koupypavel/xkboard/xkboard_mcu/firmware/examples/10_xkboard_mcu_4327/src/board_sysinit.c

/*
 * board_sysinit.c
 *
 *  Created on: 28. 6. 2021
 *      Author: xkoupy00
 */

#include "board.h"

/* The System initialization code is called prior to the application and
   initializes the board for run-time operation. Board initialization
   includes clock setup and default pin muxing configuration. */

/*****************************************************************************
 * Private types/enumerations/variables
 ****************************************************************************/

/* Structure for initial base clock states */
struct CLK_BASE_STATES {
	CHIP_CGU_BASE_CLK_T clk;	/* Base clock */
	CHIP_CGU_CLKIN_T clkin;	/* Base clock source, see UM for allowable souorces per base clock */
	bool autoblock_enab;/* Set to true to enable autoblocking on frequency change */
	bool powerdn;		/* Set to true if the base clock is initially powered down */
};

//uncomment and commnet what ever you please, is commented out for safety reason
STATIC const PINMUX_GRP_T pinmuxing[] = {

	/* Board LEDs */
	/*D5*/{0x6, 7, (SCU_MODE_INBUFF_EN | SCU_MODE_PULLUP | SCU_MODE_FUNC4)},
	/*D6*/{0x6, 9, (SCU_MODE_INBUFF_EN | SCU_MODE_PULLUP | SCU_MODE_FUNC0)},
	/*D7*/{0x6, 11, (SCU_MODE_INBUFF_EN | SCU_MODE_PULLUP | SCU_MODE_FUNC0)},

	/* Buttons */
	/*SW3*/{0x6, 3, (SCU_MODE_PULLUP | SCU_MODE_INBUFF_EN | SCU_MODE_ZIF_DIS | SCU_MODE_FUNC0)},
	/*SW4*/{0x6, 6, (SCU_MODE_PULLUP | SCU_MODE_INBUFF_EN | SCU_MODE_ZIF_DIS | SCU_MODE_FUNC0)},

	/* ARDUINO header */
//	/*0*/{0x1, 13, (SCU_MODE_INBUFF_EN | SCU_MODE_PULLUP | SCU_MODE_FUNC4)},
//	/*1*/{0x1, 14, (SCU_MODE_INBUFF_EN | SCU_MODE_PULLUP | SCU_MODE_FUNC0)},
//	/*2*/{0x1, 16, (SCU_MODE_INBUFF_EN | SCU_MODE_PULLUP | SCU_MODE_FUNC0)},
//	/*3*/{0x5, 0, (SCU_MODE_INBUFF_EN | SCU_MODE_PULLUP | SCU_MODE_FUNC4)},
	/*4*/{0x1, 17, (SCU_MODE_INBUFF_EN | SCU_MODE_PULLUP | SCU_MODE_FUNC0)},
	/*5*/{0x5, 4, (SCU_MODE_INBUFF_EN | SCU_MODE_PULLUP | SCU_MODE_FUNC0)},
	/*6*/{0x5, 5, (SCU_MODE_INBUFF_EN | SCU_MODE_PULLUP | SCU_MODE_FUNC0)},
	/*7*/{0x1, 15, (SCU_MODE_INBUFF_EN | SCU_MODE_PULLUP | SCU_MODE_FUNC0)},
	/*8*/{0x1, 18, (SCU_MODE_INBUFF_EN | SCU_MODE_PULLUP | SCU_MODE_FUNC0)},
//	/*9*/{0x5, 6, (SCU_MODE_INBUFF_EN | SCU_MODE_PULLUP | SCU_MODE_FUNC0)},
//	/*10*/{0x3, 2, (SCU_MODE_INBUFF_EN | SCU_MODE_PULLUP | SCU_MODE_FUNC0)},
//	/*11*/{0x3, 7, (SCU_MODE_INBUFF_EN | SCU_MODE_PULLUP | SCU_MODE_FUNC0)},
//	/*12*/{0x3, 6, (SCU_MODE_INBUFF_EN | SCU_MODE_PULLUP | SCU_MODE_FUNC0)},
//	/*13*/{0x3, 3, (SCU_MODE_INBUFF_EN | SCU_MODE_PULLUP | SCU_MODE_FUNC0)},

	/* LPC MCU I/O header*/
//	/*1*/{0x9, 6, (SCU_MODE_INBUFF_EN | SCU_MODE_PULLUP | SCU_MODE_FUNC0)},
//	/*2*/{0x9, 5, (SCU_MODE_INBUFF_EN | SCU_MODE_PULLUP | SCU_MODE_FUNC0)},
//	/*3*/{0x2, 0, (SCU_MODE_INBUFF_EN | SCU_MODE_PULLUP | SCU_MODE_FUNC4)},
//	/*4*/{0x2, 1, (SCU_MODE_INBUFF_EN | SCU_MODE_PULLUP | SCU_MODE_FUNC0)},
//	/*5*/{0x2, 2, (SCU_MODE_INBUFF_EN | SCU_MODE_PULLUP | SCU_MODE_FUNC0)},
//	/*6*/{0x2, 3, (SCU_MODE_INBUFF_EN | SCU_MODE_PULLUP | SCU_MODE_FUNC4)},
//	/*7*/{0x2, 4, (SCU_MODE_INBUFF_EN | SCU_MODE_PULLUP | SCU_MODE_FUNC0)},
//	/*8*/{0x2, 5, (SCU_MODE_INBUFF_EN | SCU_MODE_PULLUP | SCU_MODE_FUNC0)},
//	/*9*/{0x2, 6, (SCU_MODE_INBUFF_EN | SCU_MODE_PULLUP | SCU_MODE_FUNC0)},
//	/*10*/{0x1, 0, (SCU_MODE_INBUFF_EN | SCU_MODE_PULLUP | SCU_MODE_FUNC0)},
//	/*11*/{0x1, 3, (SCU_MODE_INBUFF_EN | SCU_MODE_PULLUP | SCU_MODE_FUNC0)},
//	/*12*/{0x1, 4, (SCU_MODE_INBUFF_EN | SCU_MODE_PULLUP | SCU_MODE_FUNC0)},
//	/*13*/{0x1, 5, (SCU_MODE_INBUFF_EN | SCU_MODE_PULLUP | SCU_MODE_FUNC0)},
//	/*14*/{0x1, 6, (SCU_MODE_INBUFF_EN | SCU_MODE_PULLUP | SCU_MODE_FUNC0)},
//	/*15*/{0x1, 7, (SCU_MODE_INBUFF_EN | SCU_MODE_PULLUP | SCU_MODE_FUNC0)},
//	/*16*/{0x1, 8, (SCU_MODE_INBUFF_EN | SCU_MODE_PULLUP | SCU_MODE_FUNC0)},
//	/*17*/{0x1, 9, (SCU_MODE_INBUFF_EN | SCU_MODE_PULLUP | SCU_MODE_FUNC0)},
//	/*18*/{0x1, 10, (SCU_MODE_INBUFF_EN | SCU_MODE_PULLUP | SCU_MODE_FUNC0)},
//	/*19*/{0x1, 11, (SCU_MODE_INBUFF_EN | SCU_MODE_PULLUP | SCU_MODE_FUNC0)},
//	/*20*/{0x1, 12, (SCU_MODE_INBUFF_EN | SCU_MODE_PULLUP | SCU_MODE_FUNC0)},
};
/*****************************************************************************
 * Public types/enumerations/variables
 ****************************************************************************/

/*****************************************************************************
 * Private functions
 ****************************************************************************/

/*****************************************************************************
 * Public functions
 ****************************************************************************/

/* Sets up system pin muxing to GPIO*/
void Board_SetupMuxing(void)
{
	/* Setup system level pin muxing */
	Chip_SCU_SetPinMuxing(pinmuxing, sizeof(pinmuxing) / sizeof(PINMUX_GRP_T));
}

void Board_SetupClocking()
{
	 Chip_SetupCoreClock( CLKIN_CRYSTAL , 12000000, true);
}

/* Set up and initialize hardware prior to call to main */
void Board_SystemInit(void)
{
	/* Setup system clocking and memory. This is done early to allow the
	   application and tools to clear memory and use scatter loading to
	   external memory. */
	Board_SetupMuxing();
	Board_SetupClocking();
}
